GayaniHewasura/In19-S3-EN2090---Laboratory-Practice---II/function generator enclosure/2_way_switch/Renderings/perilla.JPG

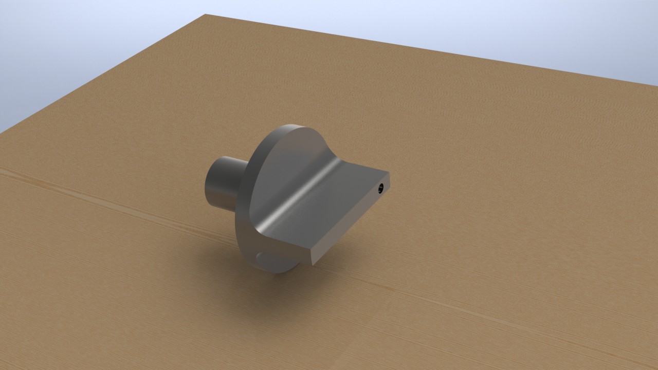
function generator enclosure/2_way_switch/Renderings/perilla.JPG
