GayaniHewasura/In19-S3-EN2090---Laboratory-Practice---II/function generator enclosure/c_k_continous/Potentiometer knob_A15x17-PK-AB-K-I__02.png

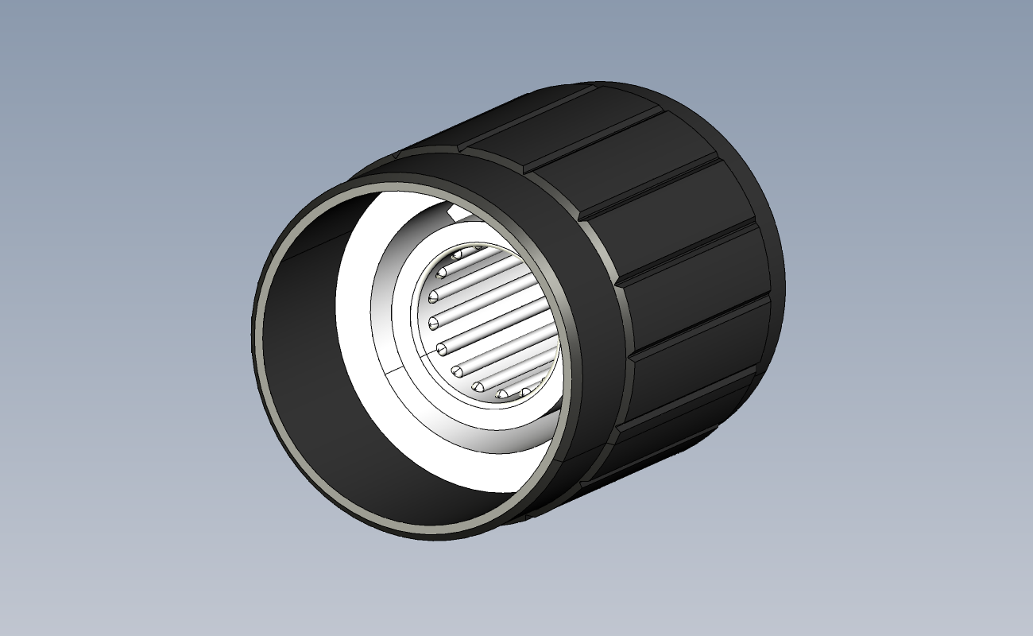
function generator enclosure/c_k_continous/Potentiometer knob_A15x17-PK-AB-K-I__02.png
