GayaniHewasura/In19-S3-EN2090---Laboratory-Practice---II/function generator enclosure/mini/61crGb5nilS._SX522_.jpg

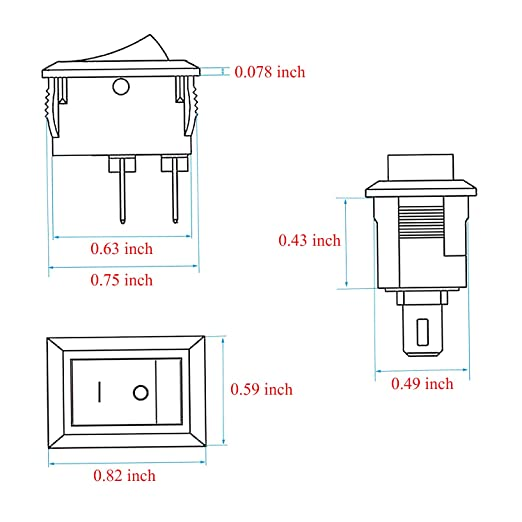
function generator enclosure/mini/61crGb5nilS._SX522_.jpg
